AriaAbd1/Fume-Extracter/images/IMG_6583.jpg

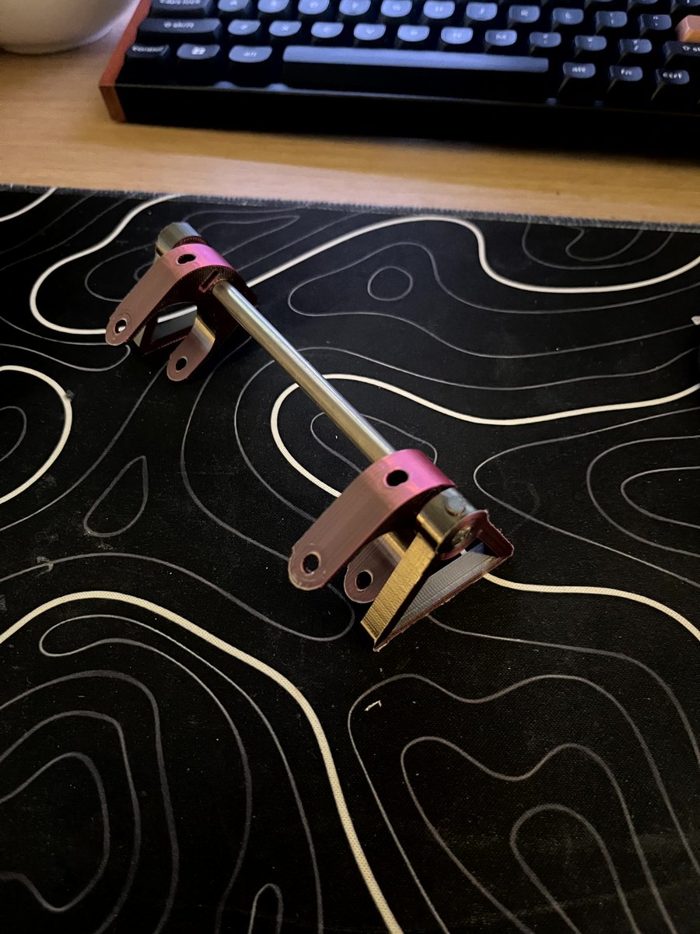
images/IMG_6583.jpg
