AriaAbd1/Fume-Extracter/images/IMG_6584.jpg

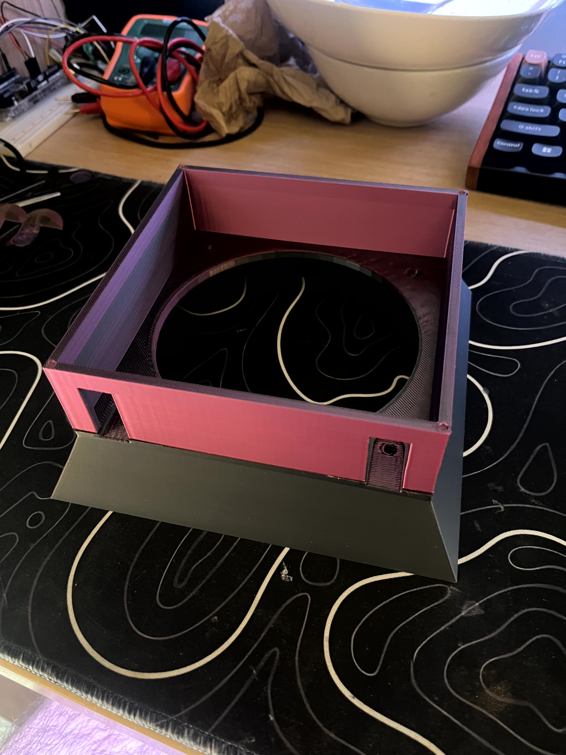
images/IMG_6584.jpg
