AriaAbd1/Fume-Extracter/images/IMG_6585.jpg

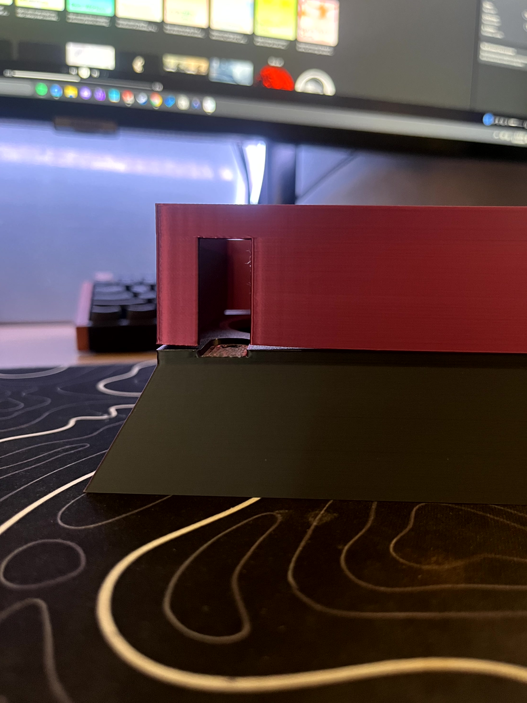
images/IMG_6585.jpg
