AriaAbd1/Fume-Extracter/images/IMG_6586.jpg

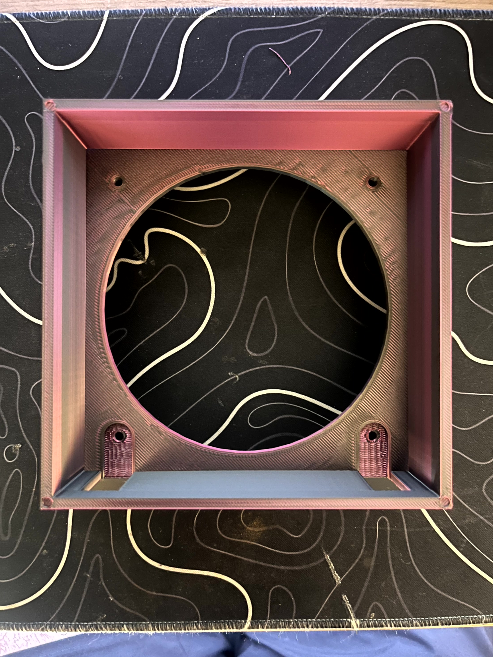
images/IMG_6586.jpg
