AriaAbd1/Fume-Extracter/images/IMG_6587.jpg

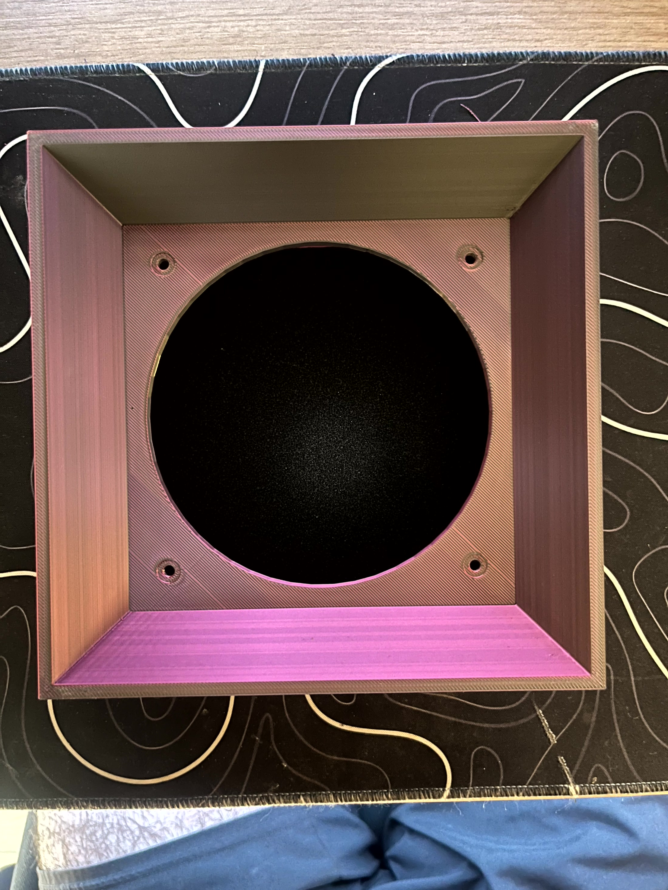
images/IMG_6587.jpg
