AriaAbd1/Fume-Extracter/images/IMG_6588.jpg

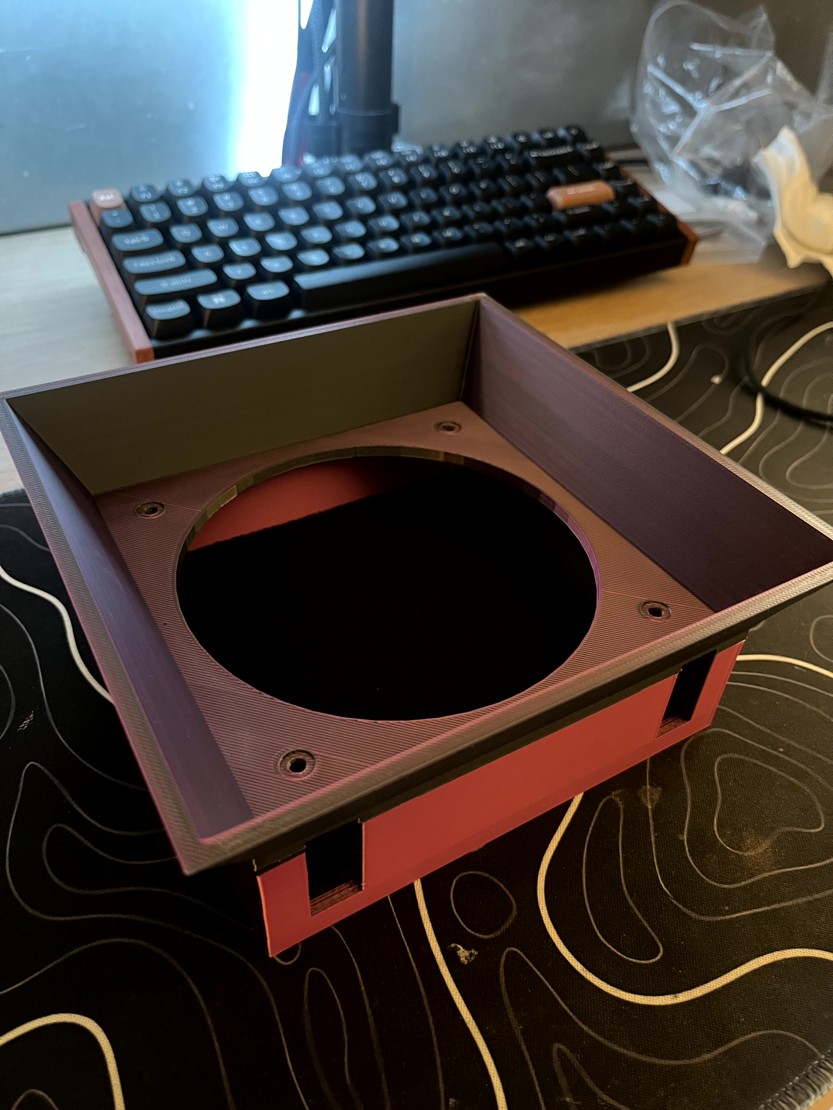
images/IMG_6588.jpg
