AriaAbd1/Fume-Extracter/images/IMG_6589.jpg

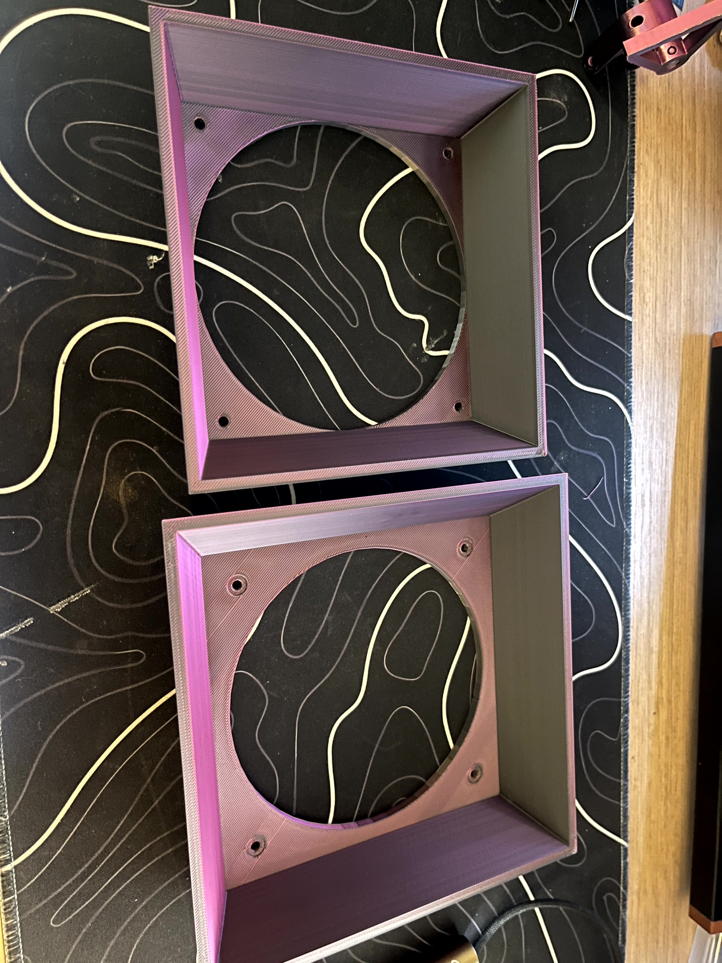
images/IMG_6589.jpg
