AriaAbd1/Fume-Extracter/images/IMG_6590.jpg

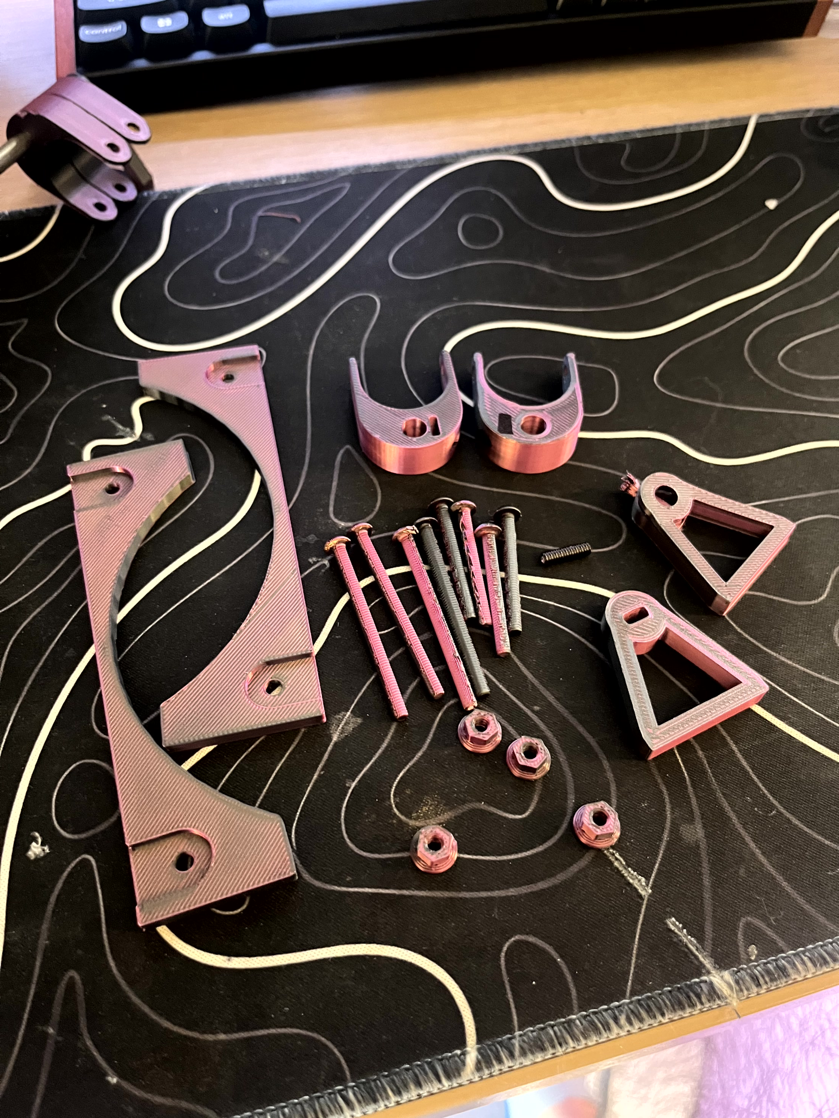
images/IMG_6590.jpg
