AriaAbd1/Fume-Extracter/images/IMG_6591.jpg

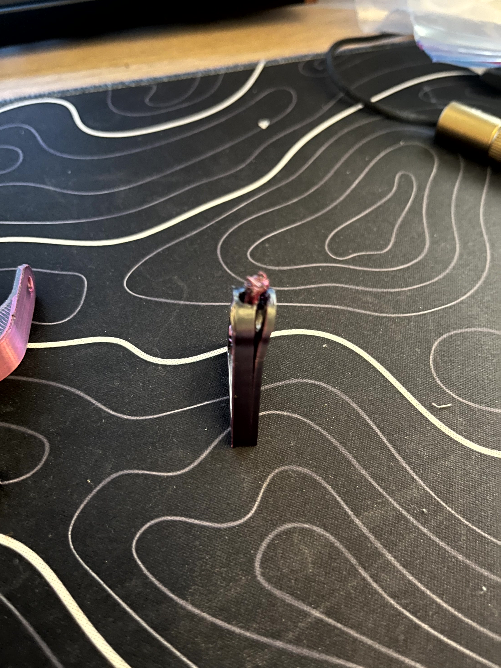
images/IMG_6591.jpg
