AriaAbd1/Fume-Extracter/images/IMG_6592.jpg

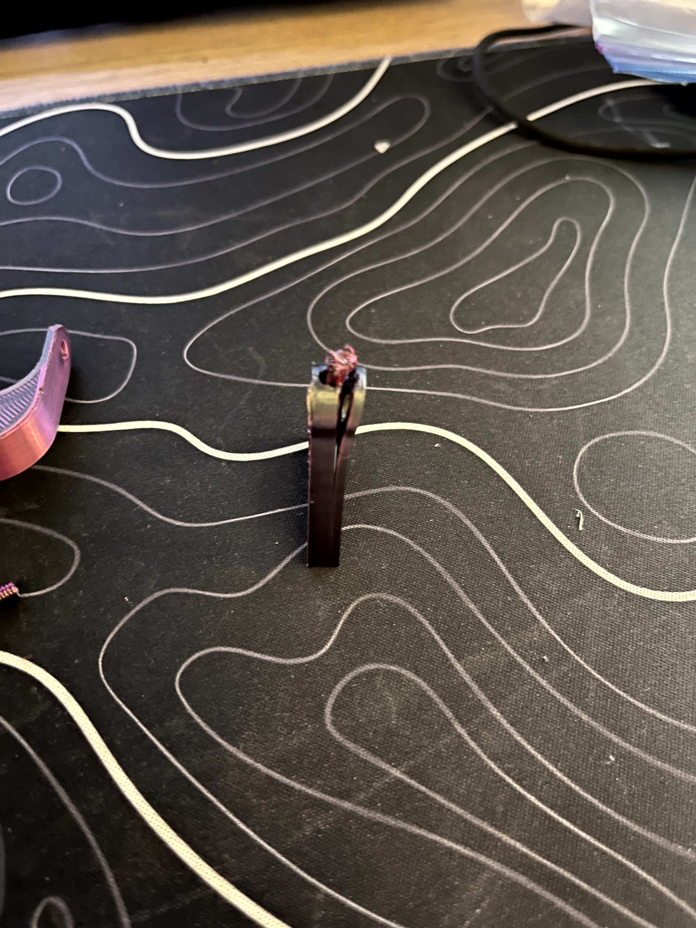
images/IMG_6592.jpg
