AriaAbd1/Fume-Extracter/images/IMG_6593.jpg

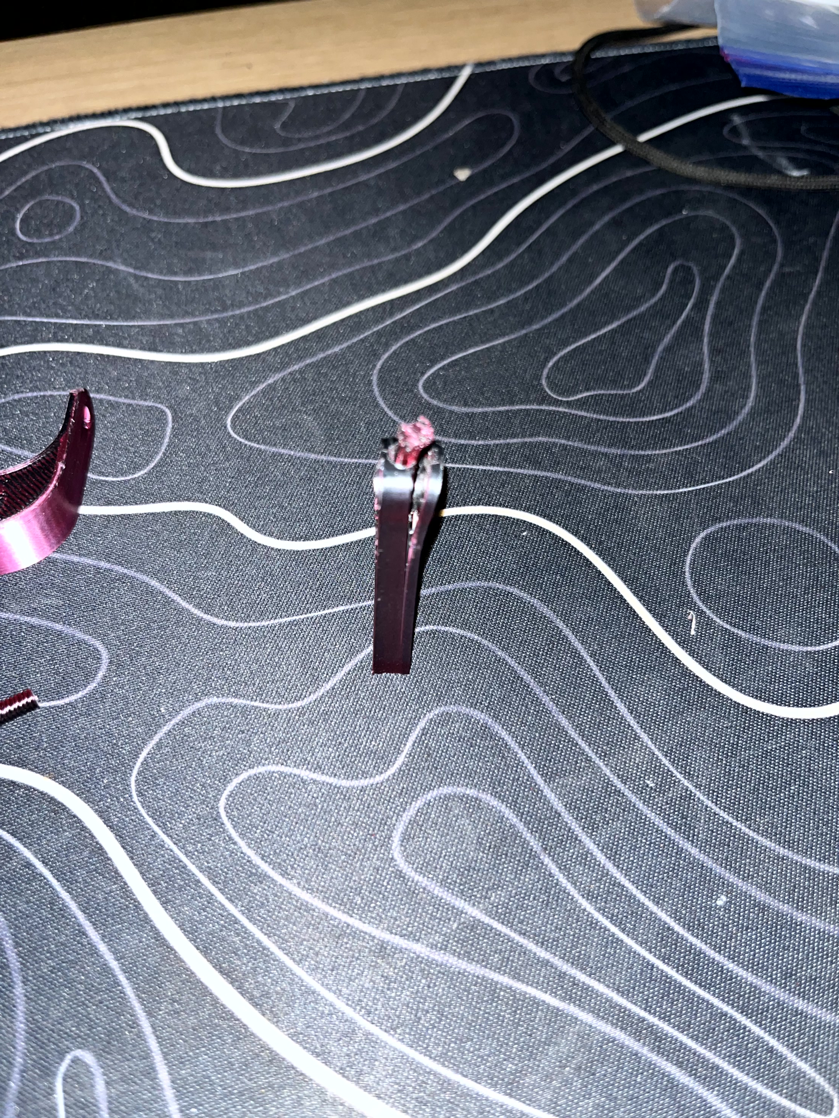
images/IMG_6593.jpg
