AriaAbd1/Fume-Extracter/images/IMG_6594.jpg

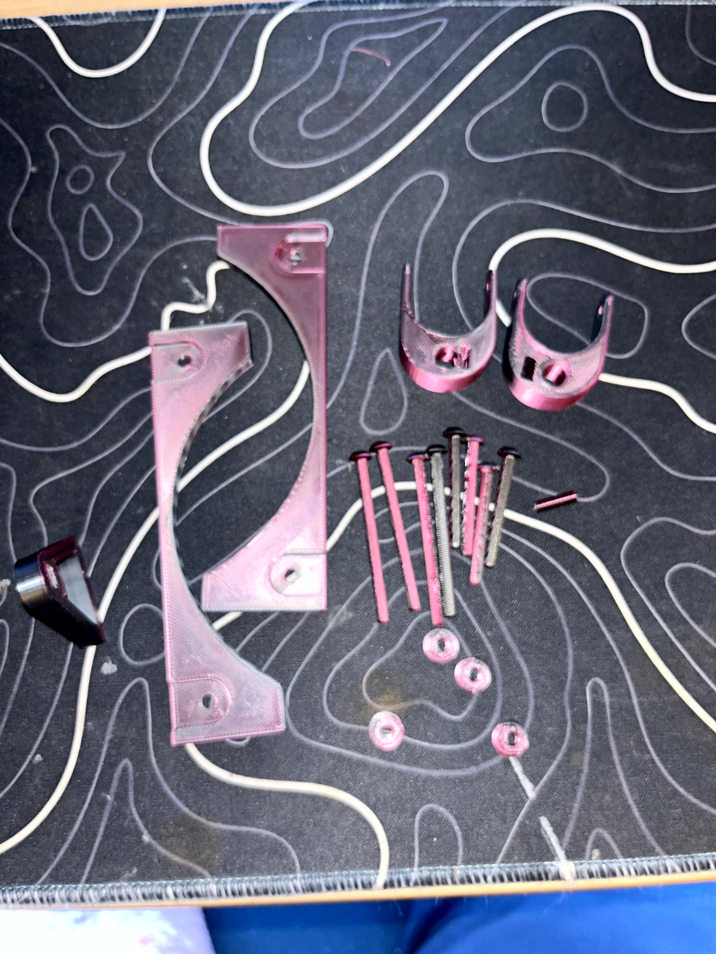
images/IMG_6594.jpg
