AriaAbd1/Fume-Extracter/images/IMG_6595.jpg

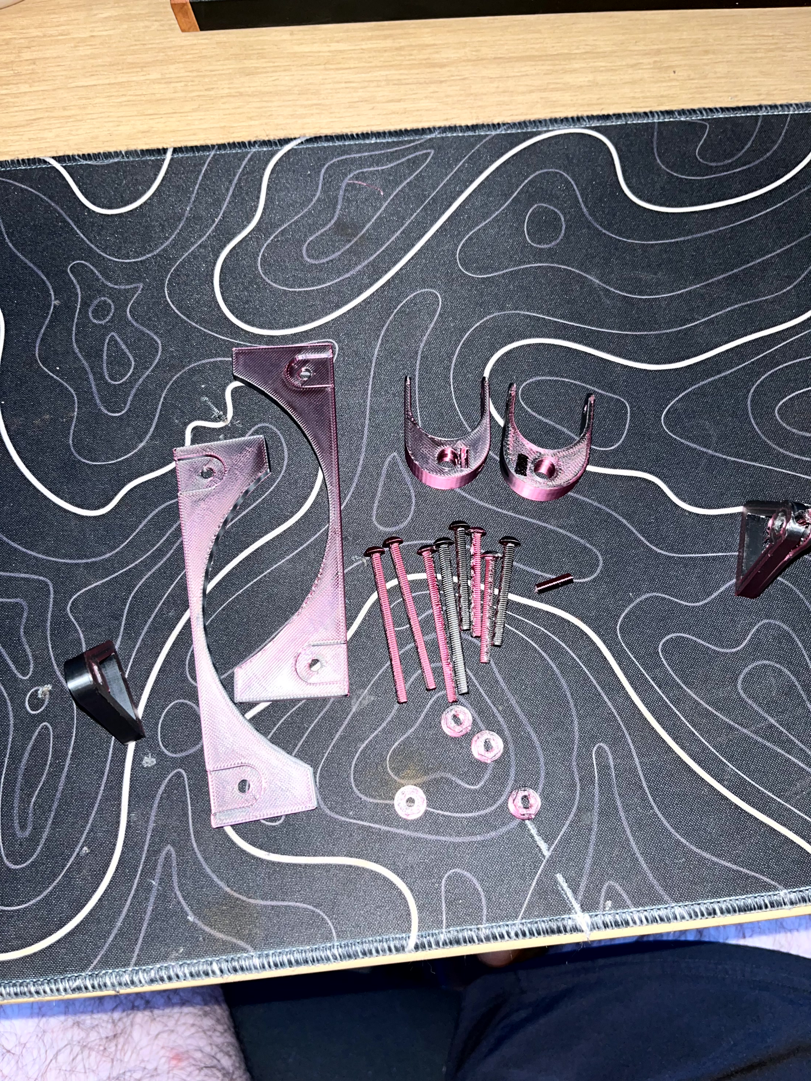
images/IMG_6595.jpg
