AriaAbd1/Fume-Extracter/images/IMG_6596.jpg

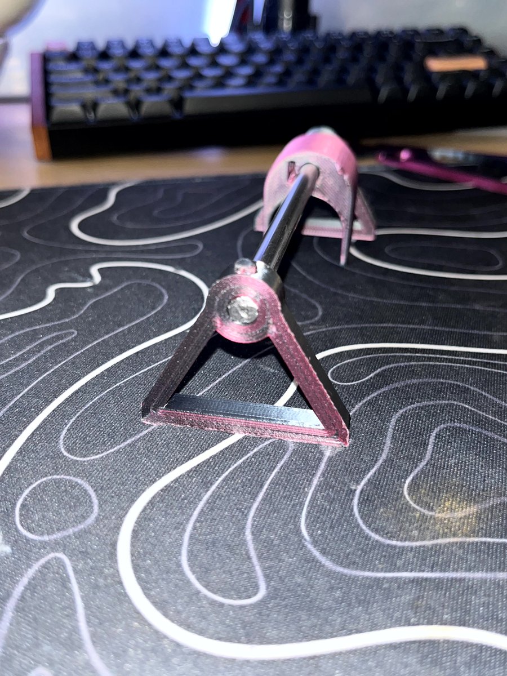
images/IMG_6596.jpg
