AriaAbd1/Fume-Extracter/images/IMG_6597.jpg

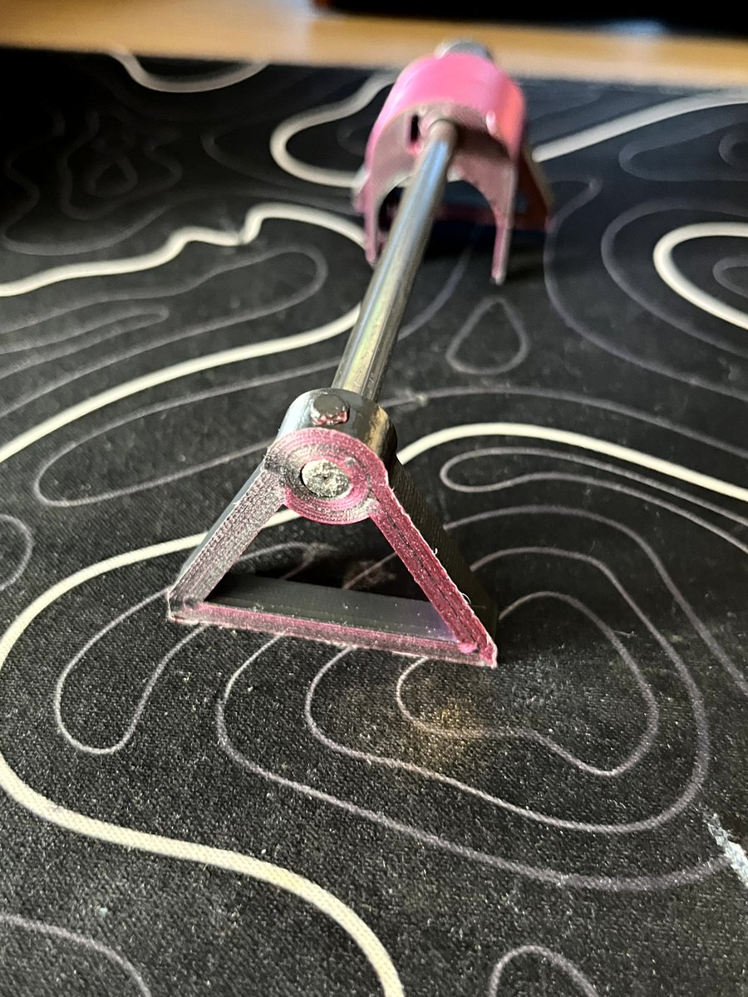
images/IMG_6597.jpg
