AriaAbd1/Fume-Extracter/images/IMG_6598.jpg

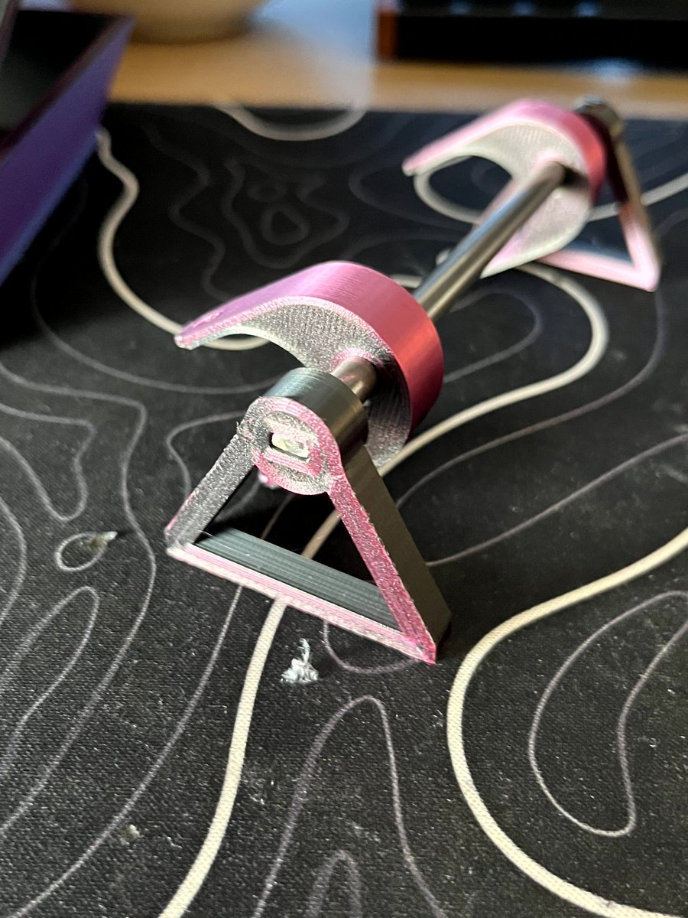
images/IMG_6598.jpg
