AriaAbd1/Fume-Extracter/images/IMG_6599.jpg

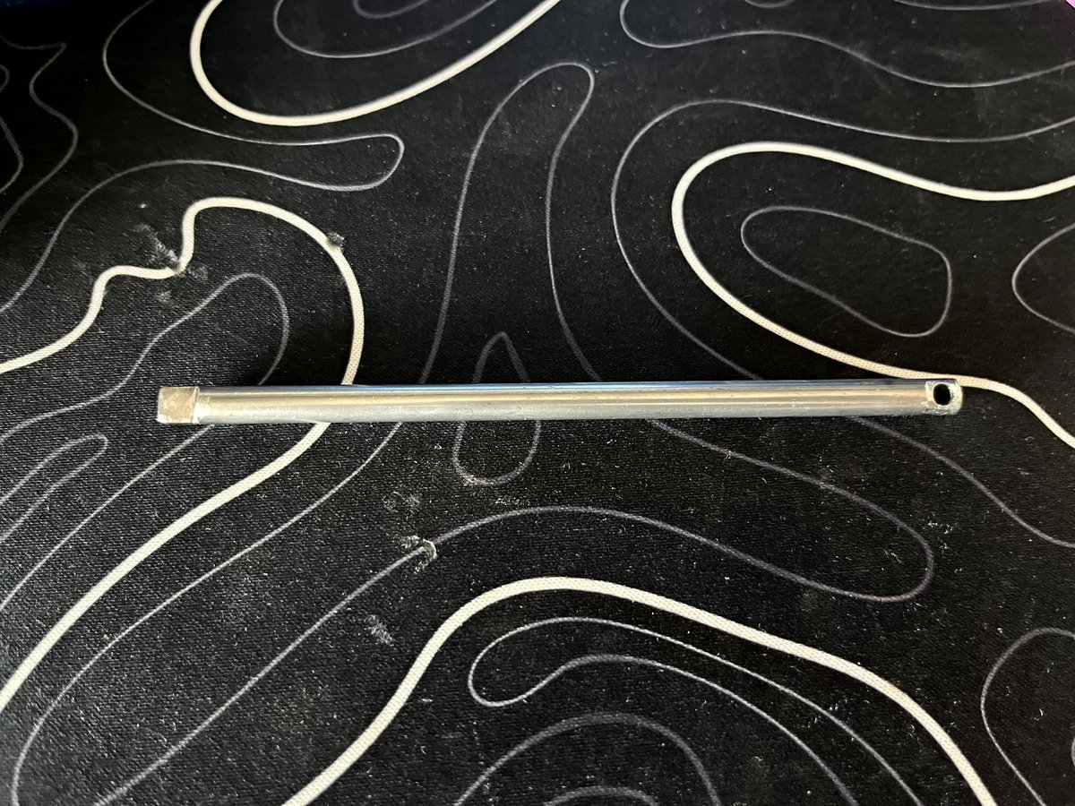
images/IMG_6599.jpg
