AriaAbd1/Fume-Extracter/images/IMG_6600.jpg

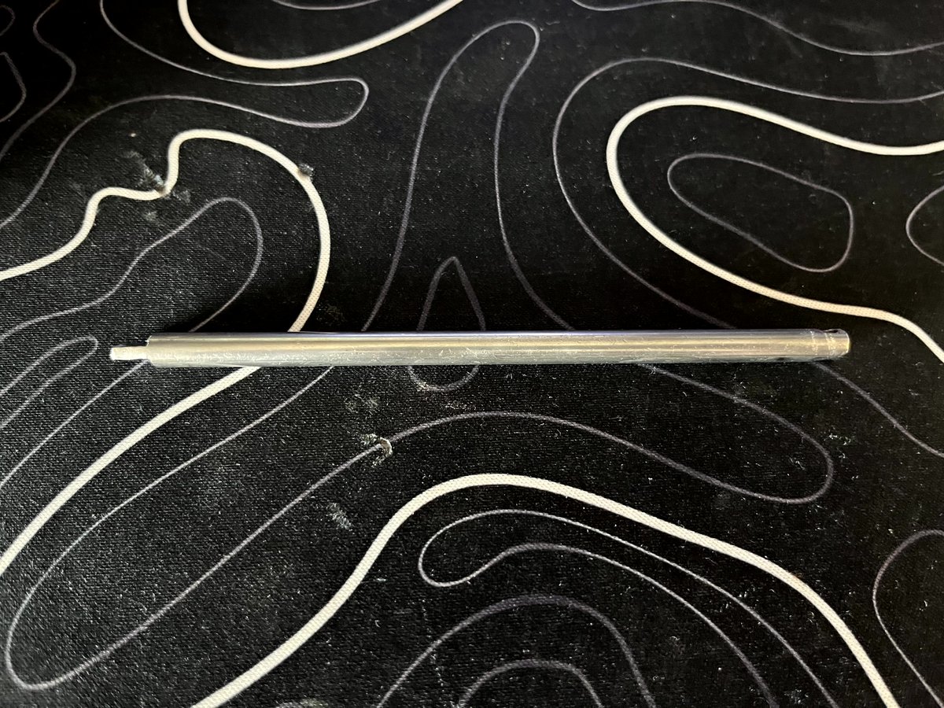
images/IMG_6600.jpg
