AriaAbd1/Fume-Extracter/images/IMG_6601.jpg

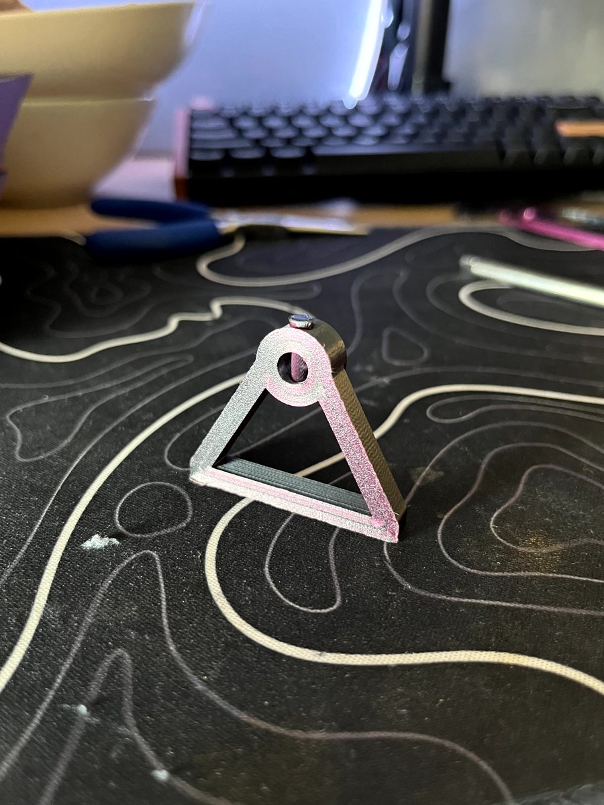
images/IMG_6601.jpg
