AriaAbd1/Fume-Extracter/images/IMG_6602.jpg

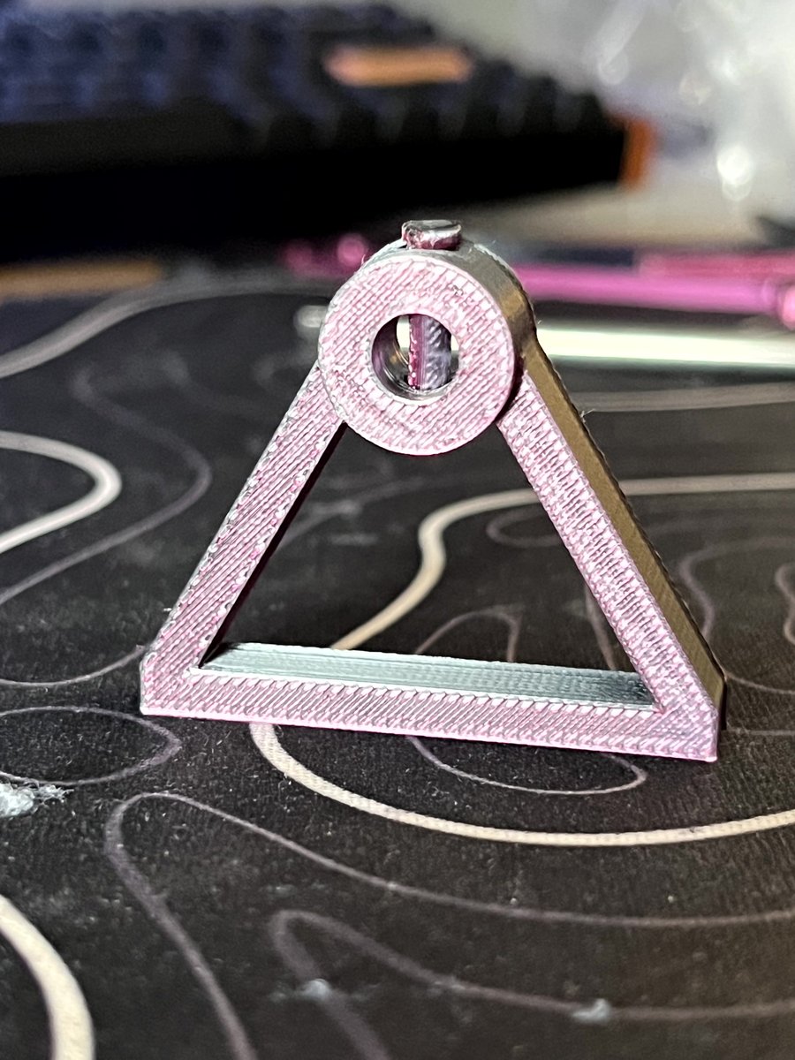
images/IMG_6602.jpg
