AriaAbd1/Fume-Extracter/images/IMG_6603.jpg

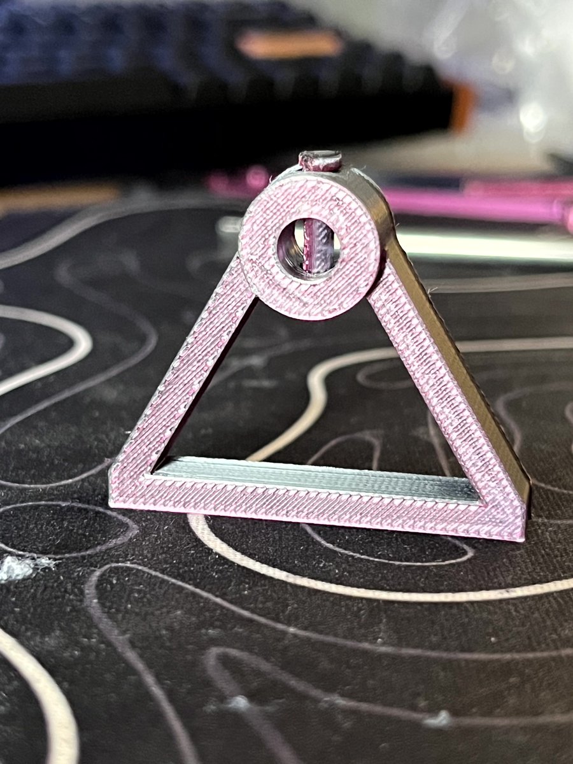
images/IMG_6603.jpg
