AriaAbd1/Fume-Extracter/images/IMG_6604.jpg

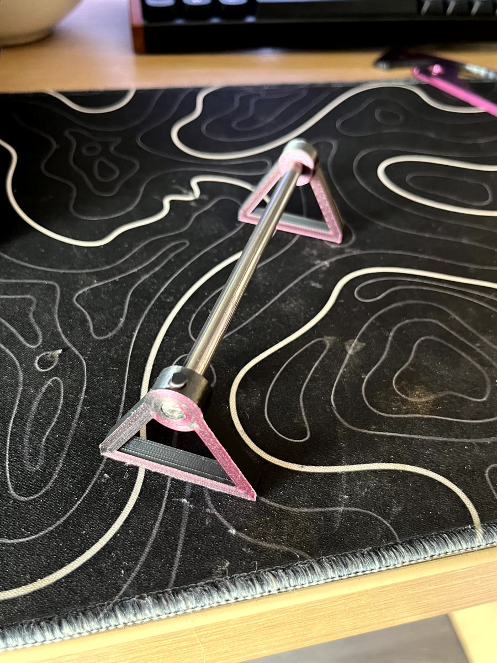
images/IMG_6604.jpg
