AriaAbd1/Fume-Extracter/images/IMG_6618.jpg

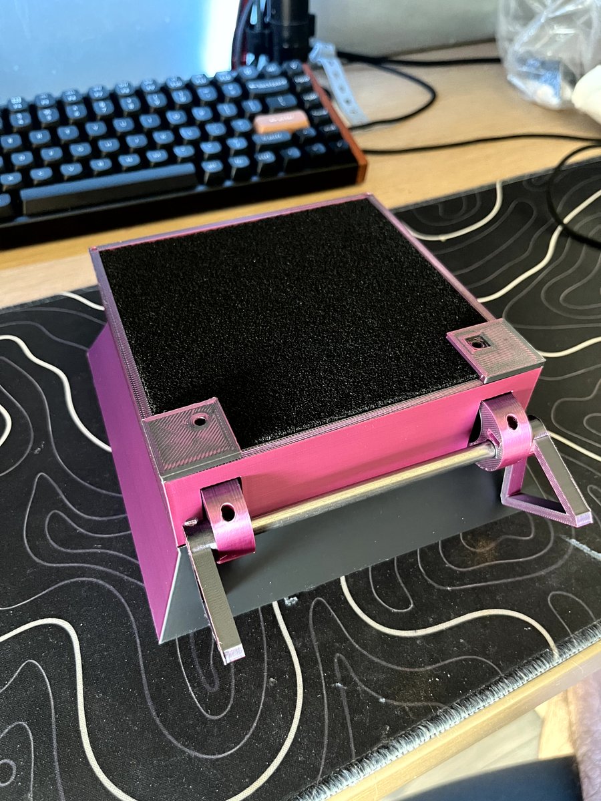
images/IMG_6618.jpg
