AriaAbd1/Fume-Extracter/images/IMG_6619.jpg

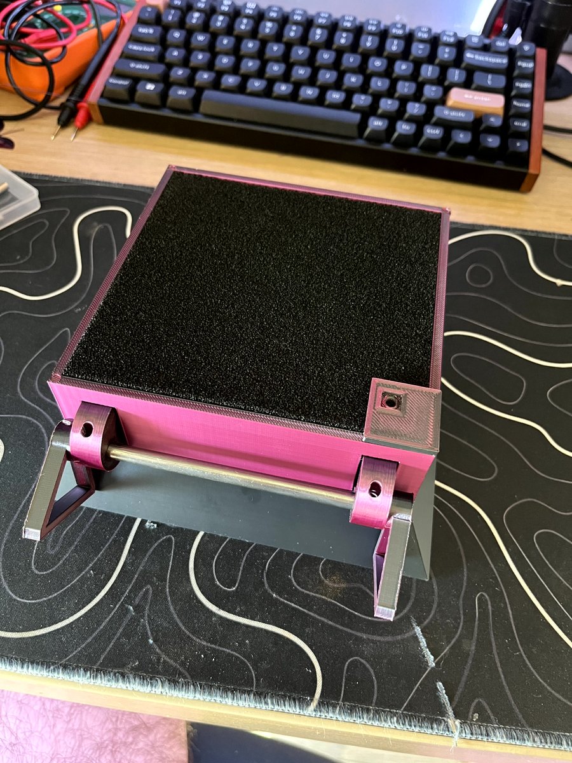
images/IMG_6619.jpg
