AriaAbd1/Fume-Extracter/images/IMG_6620.jpg

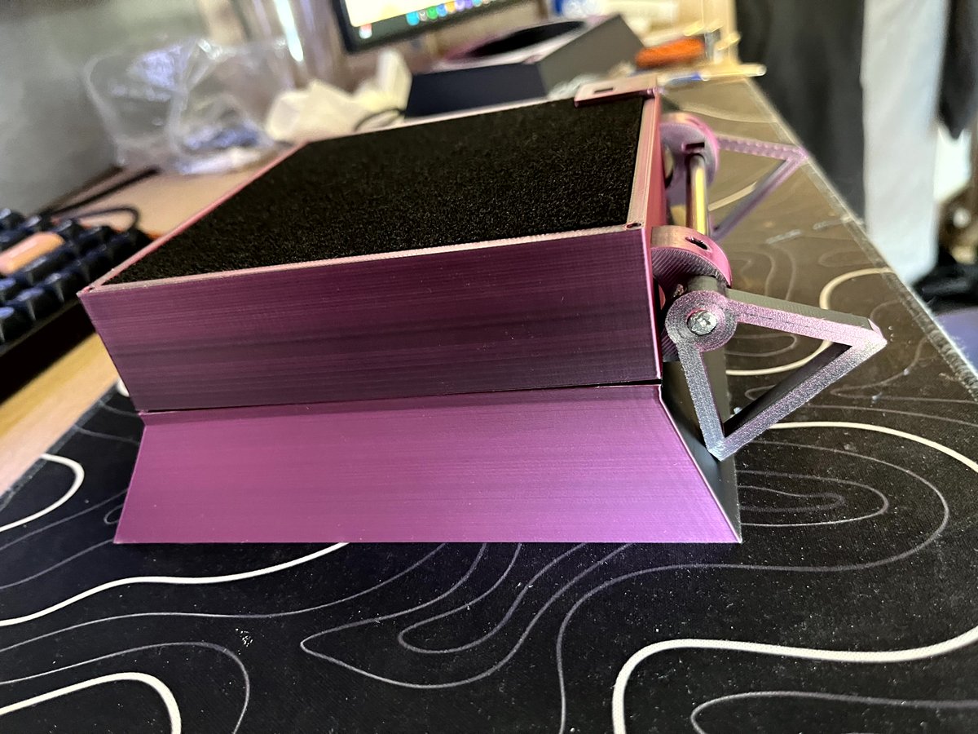
images/IMG_6620.jpg
