AriaAbd1/Fume-Extracter/images/IMG_6621.jpg

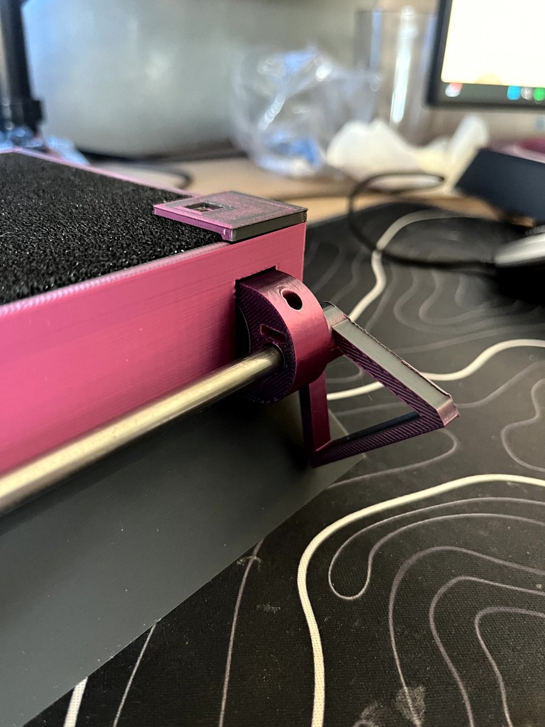
images/IMG_6621.jpg
