AriaAbd1/Fume-Extracter/images/IMG_6622.jpg

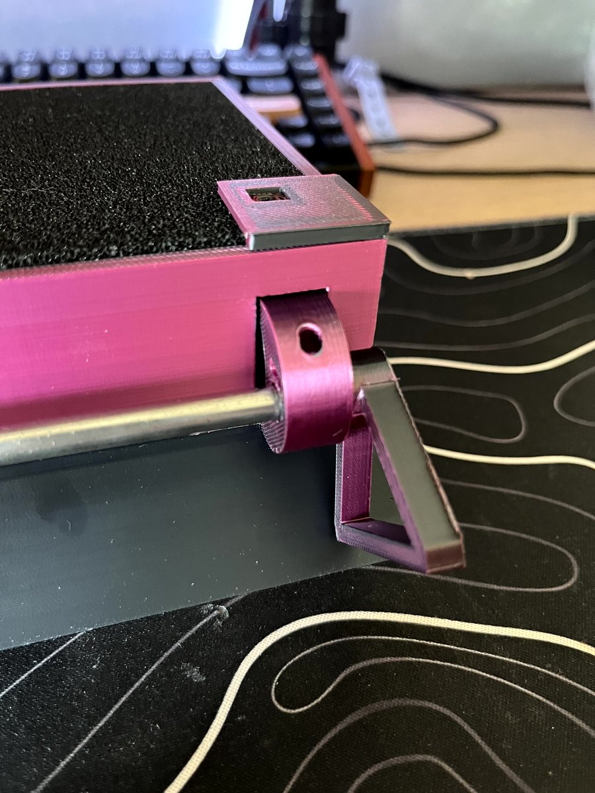
images/IMG_6622.jpg
