AriaAbd1/Fume-Extracter/images/IMG_6623.jpg

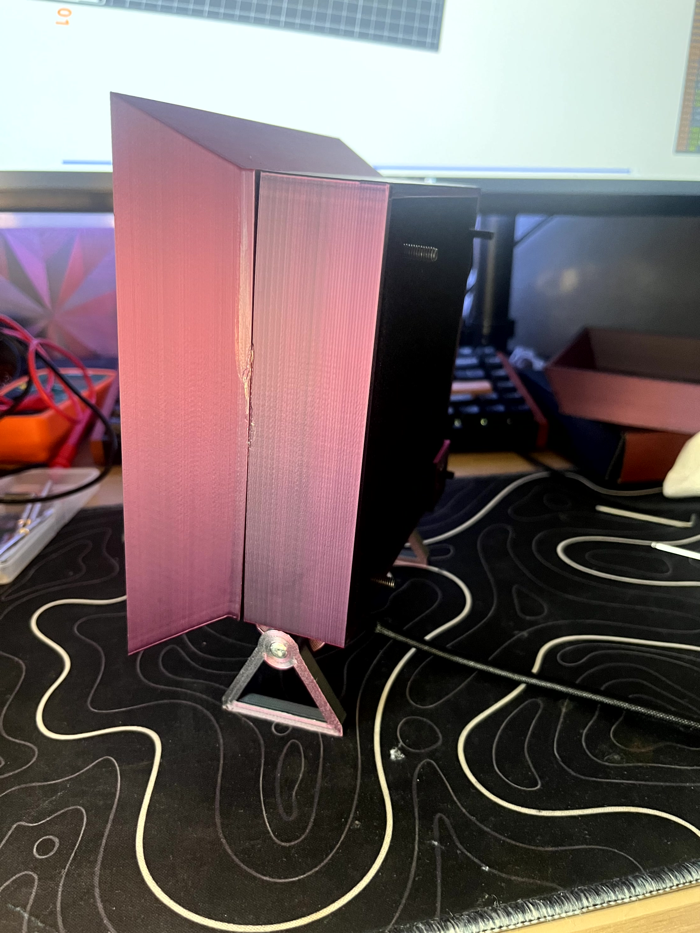
images/IMG_6623.jpg
