AriaAbd1/Fume-Extracter/images/IMG_6624.jpg

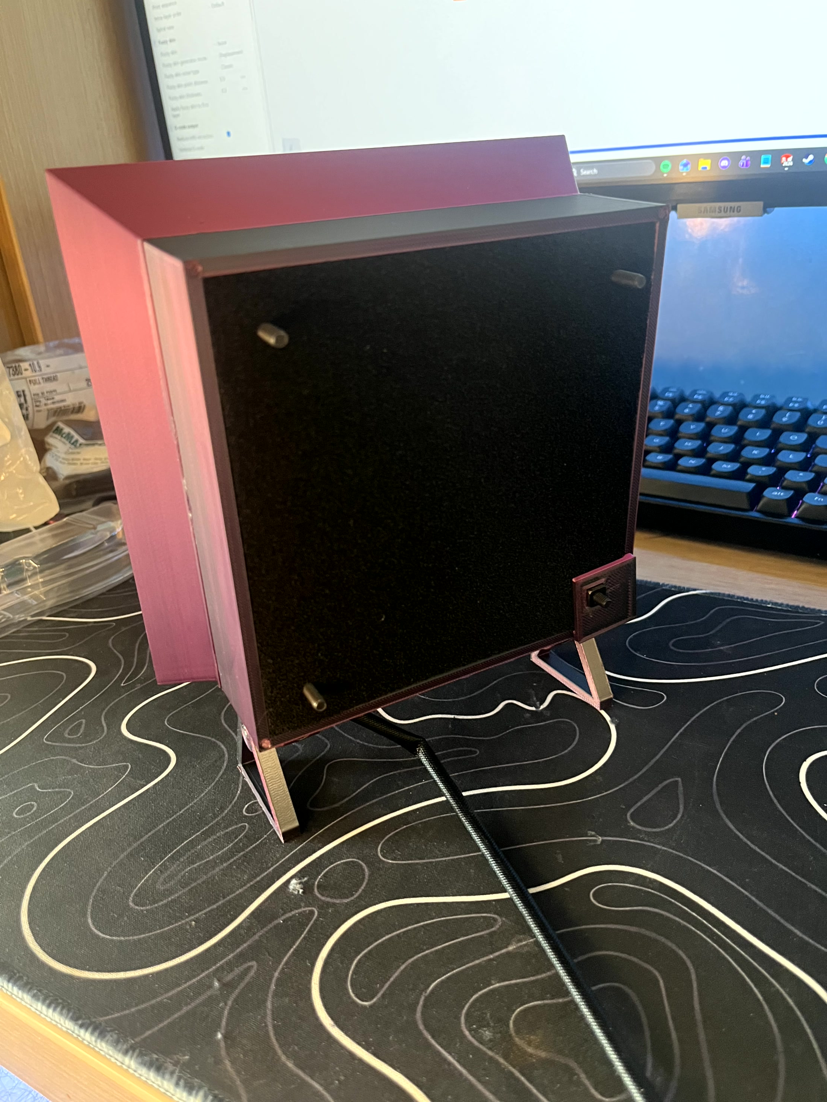
images/IMG_6624.jpg
