AriaAbd1/Fume-Extracter/images/IMG_6625.jpg

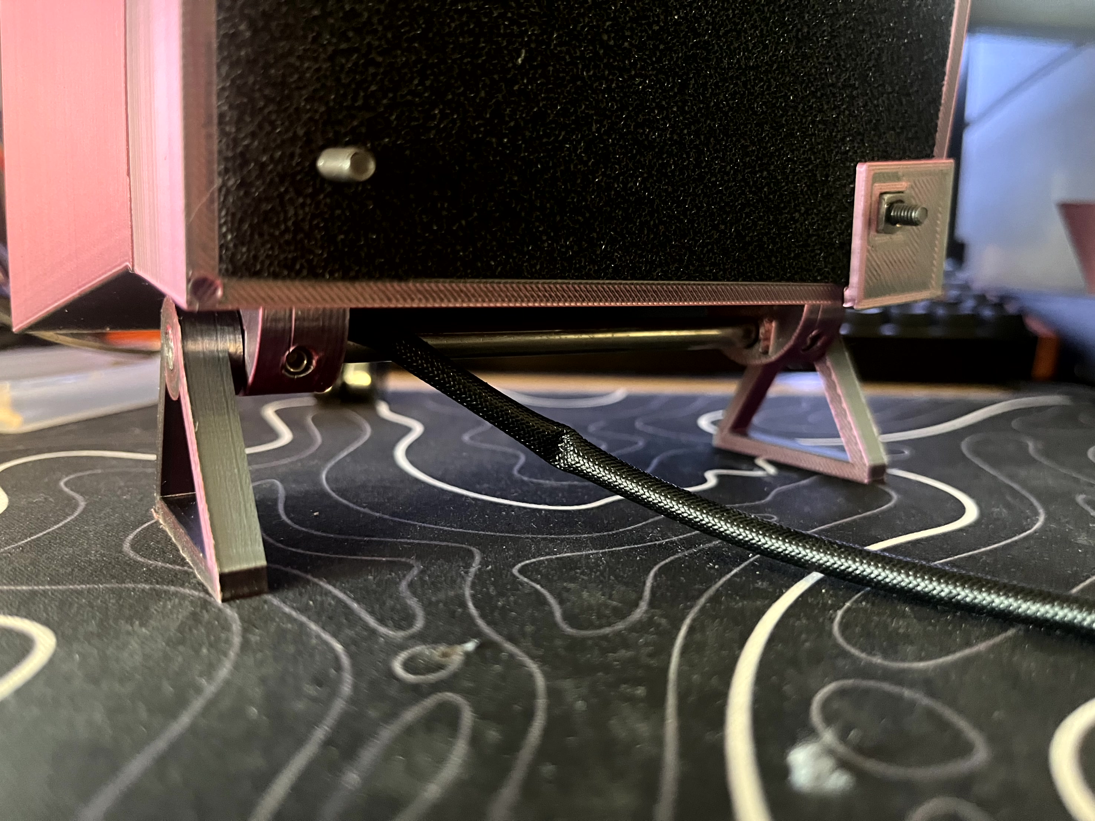
images/IMG_6625.jpg
