AriaAbd1/Fume-Extracter/images/IMG_6626.jpg

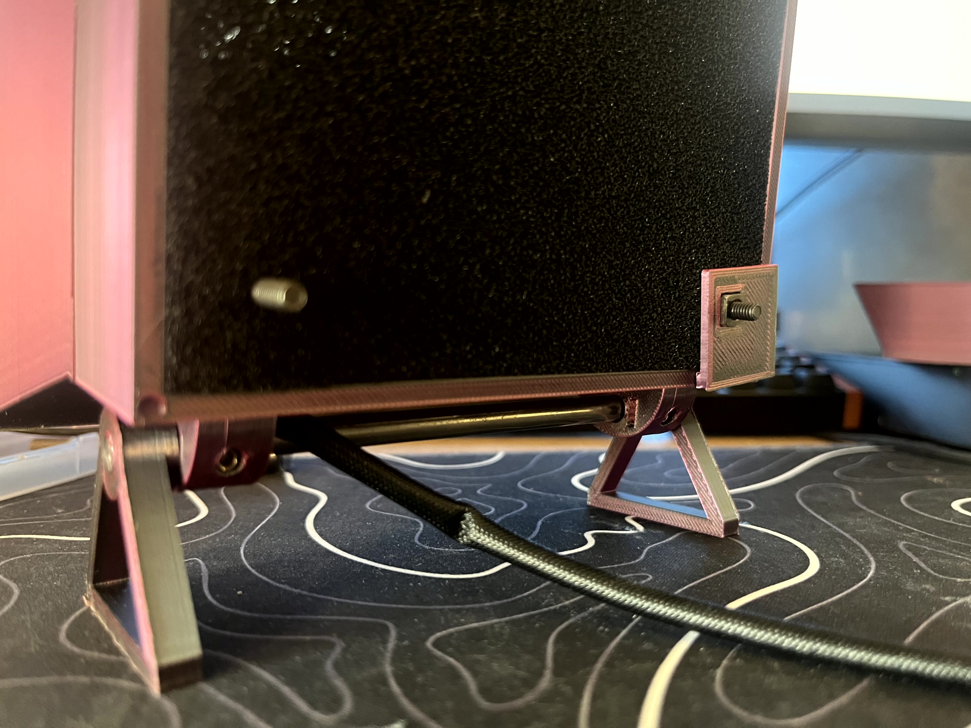
images/IMG_6626.jpg
