AriaAbd1/Fume-Extracter/images/IMG_6627.jpg

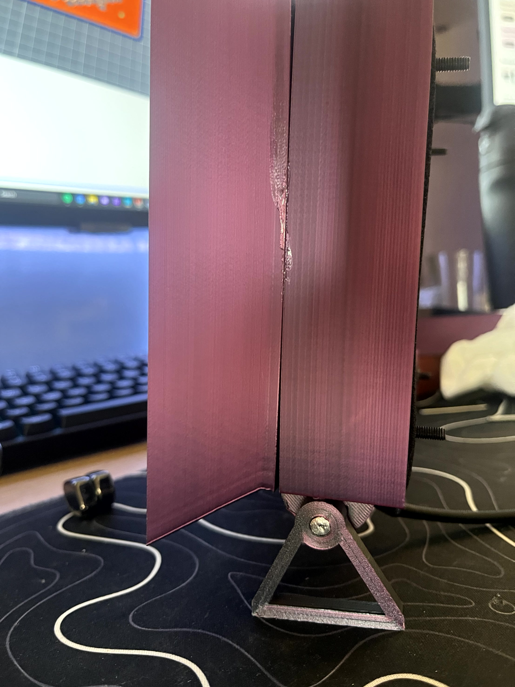
images/IMG_6627.jpg
