AriaAbd1/Fume-Extracter/images/IMG_6628.jpg

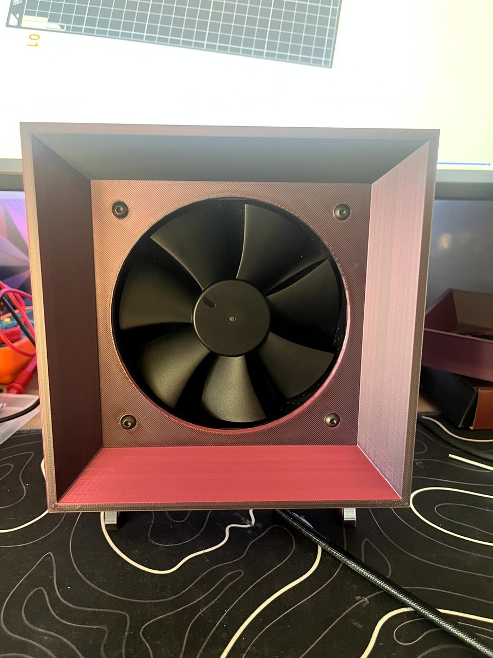
images/IMG_6628.jpg
