AriaAbd1/Fume-Extracter/images/IMG_6629.jpg

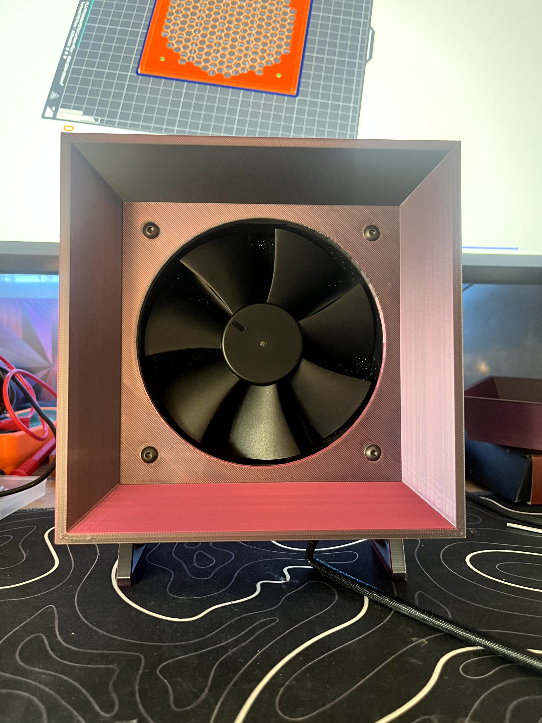
images/IMG_6629.jpg
