AriaAbd1/Fume-Extracter/images/IMG_6630.jpg

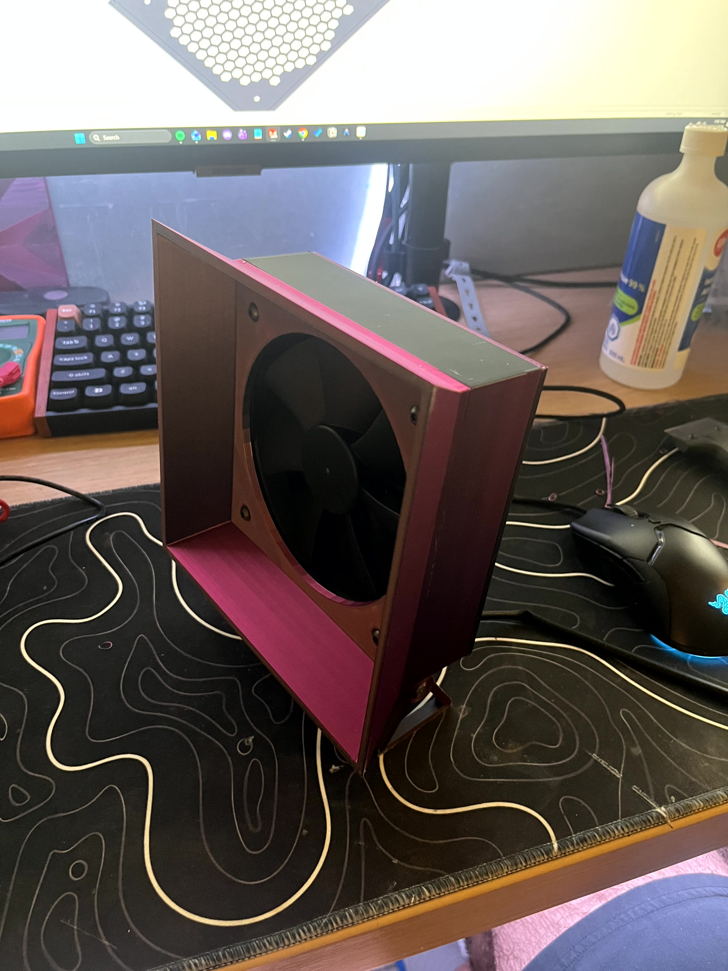
images/IMG_6630.jpg
