AriaAbd1/Fume-Extracter/images/IMG_6631.jpg

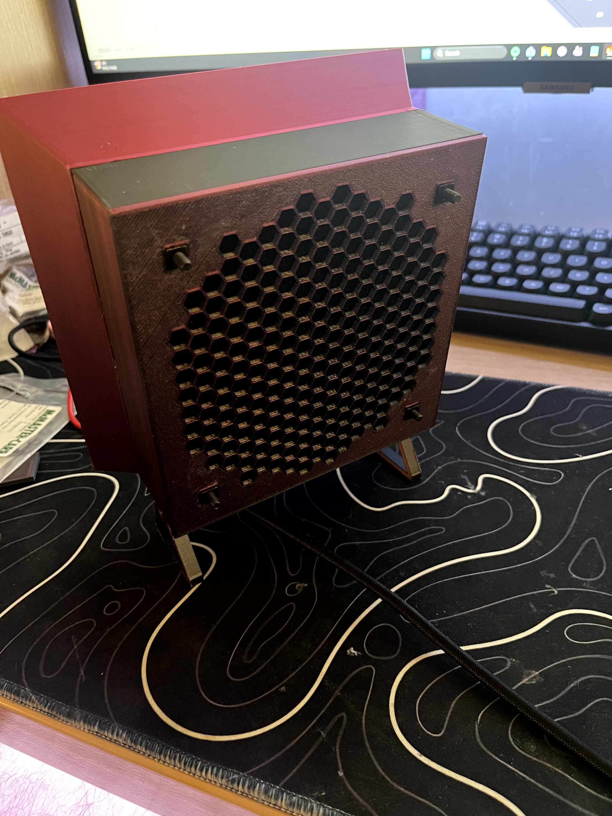
images/IMG_6631.jpg
