AriaAbd1/Fume-Extracter/images/IMG_6632.jpg

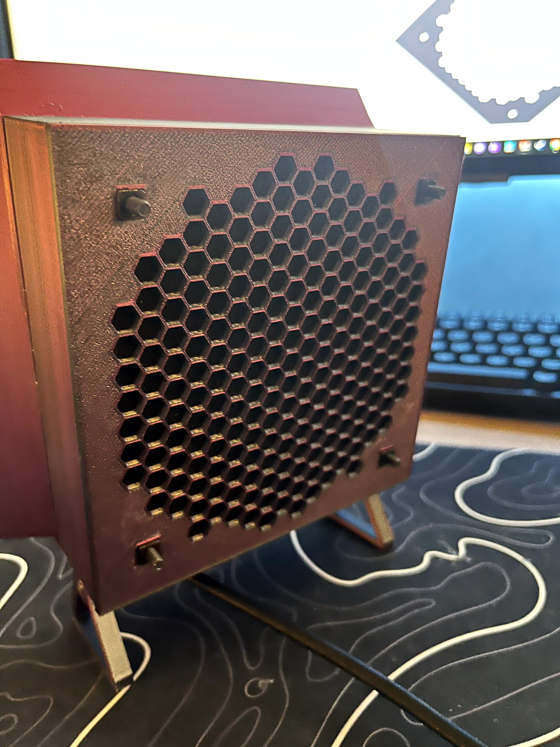
images/IMG_6632.jpg
