AriaAbd1/Fume-Extracter/images/IMG_6633.jpg

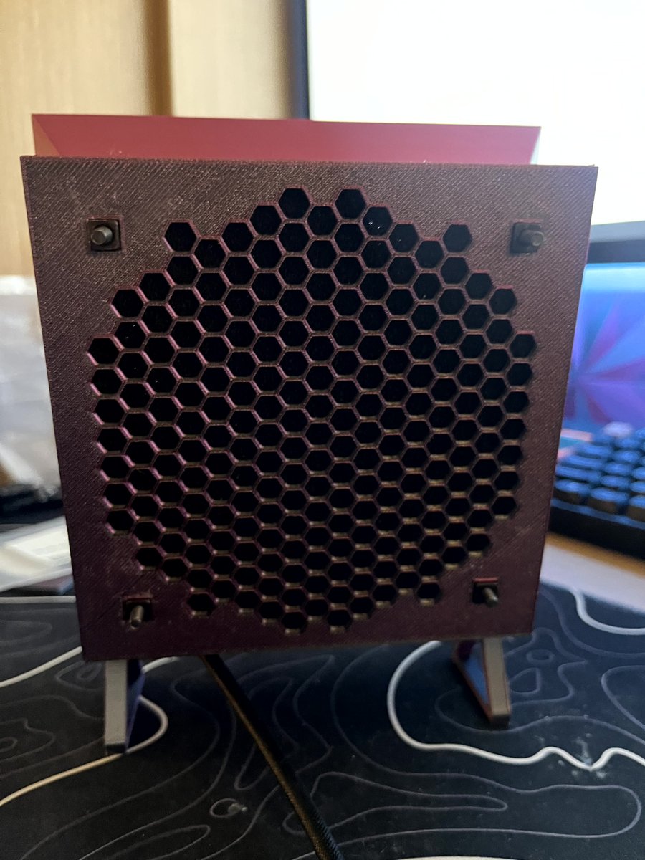
images/IMG_6633.jpg
