AriaAbd1/Fume-Extracter/images/IMG_6634.jpg

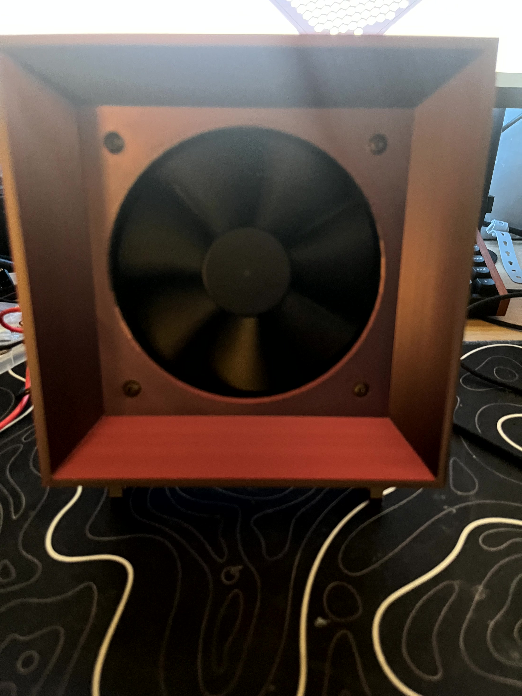
images/IMG_6634.jpg
