AriaAbd1/Fume-Extracter/images/IMG_6635.jpg

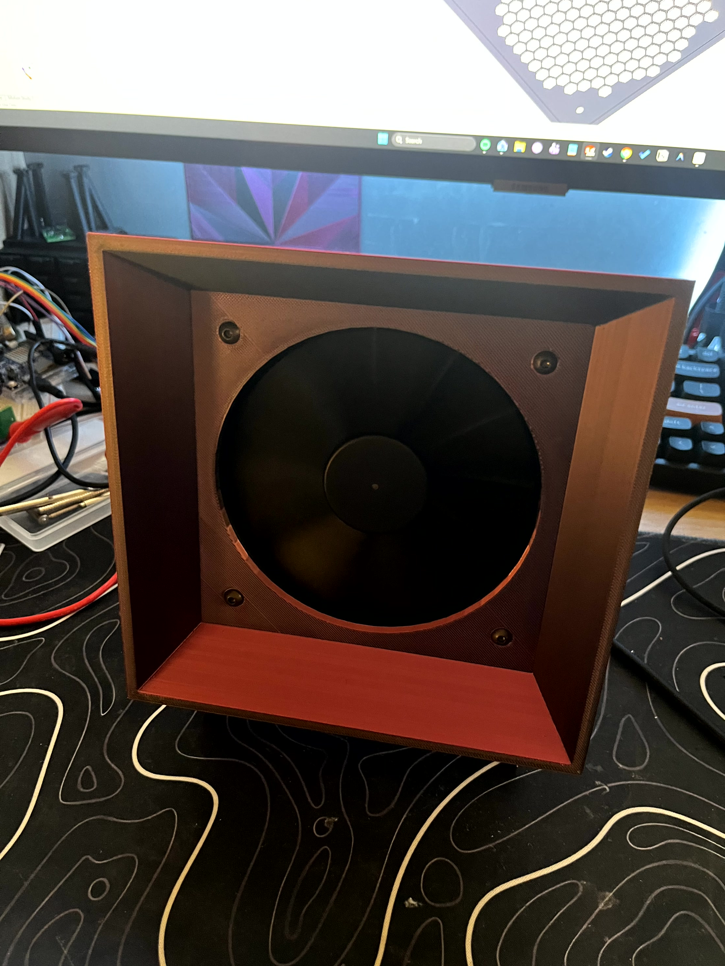
images/IMG_6635.jpg
