AriaAbd1/Fume-Extracter/images/IMG_6637.jpg

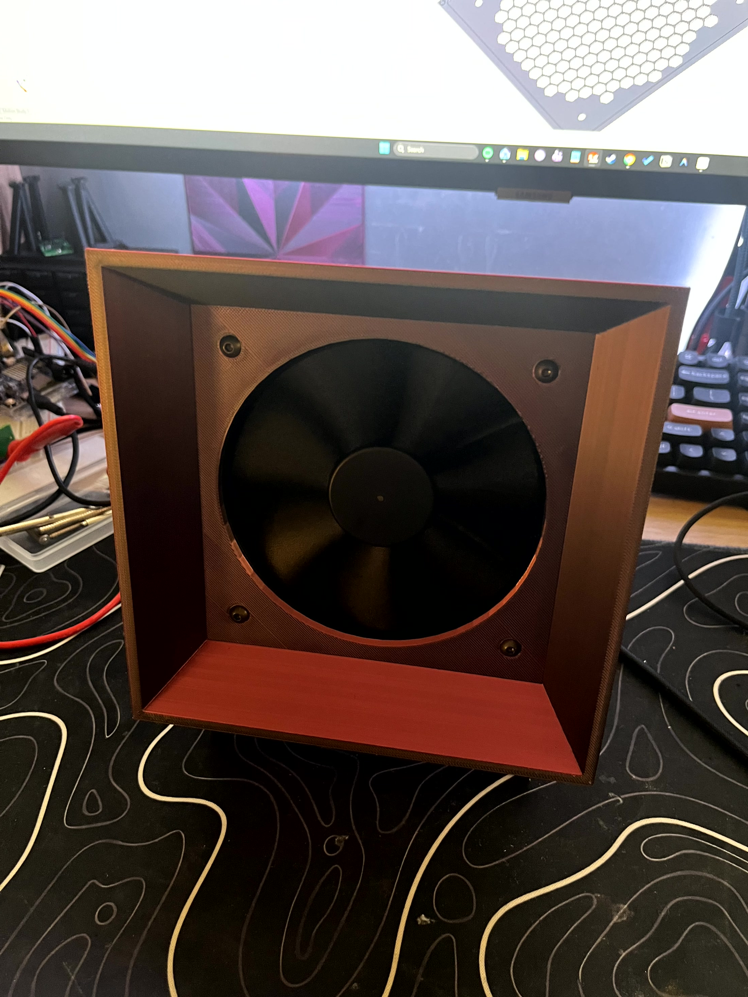
images/IMG_6637.jpg
