AriaAbd1/Fume-Extracter/images/IMG_6640.jpg

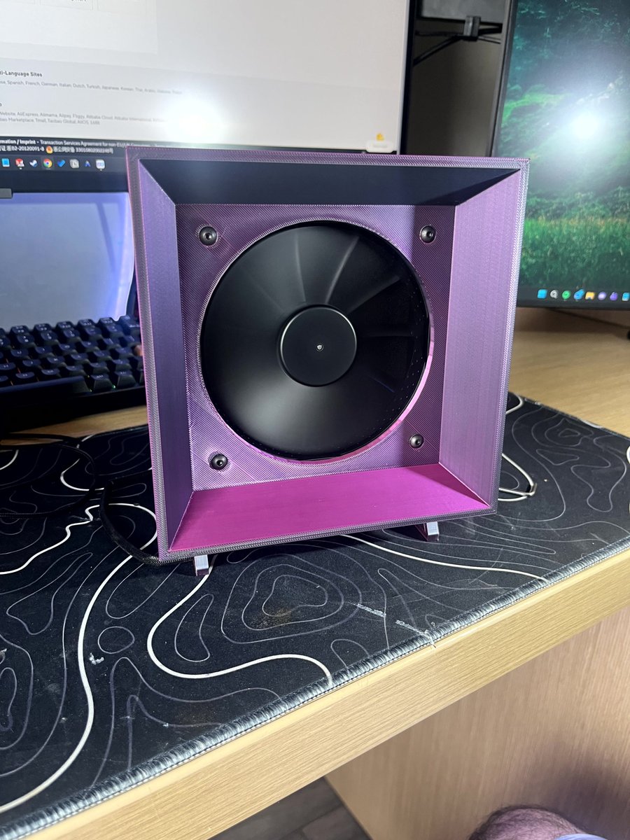
images/IMG_6640.jpg
