AriaAbd1/Fume-Extracter/images/IMG_6641.jpg

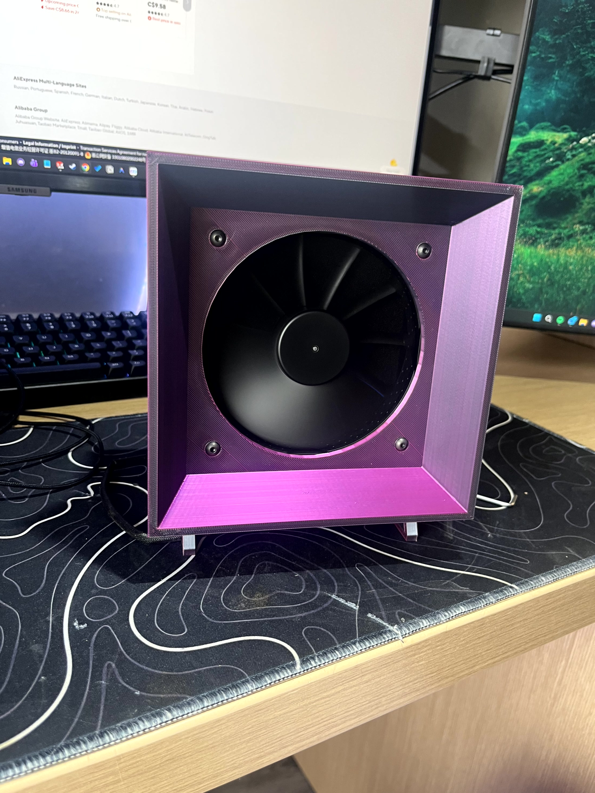
images/IMG_6641.jpg
