AriaAbd1/Fume-Extracter/images/IMG_6642.jpg

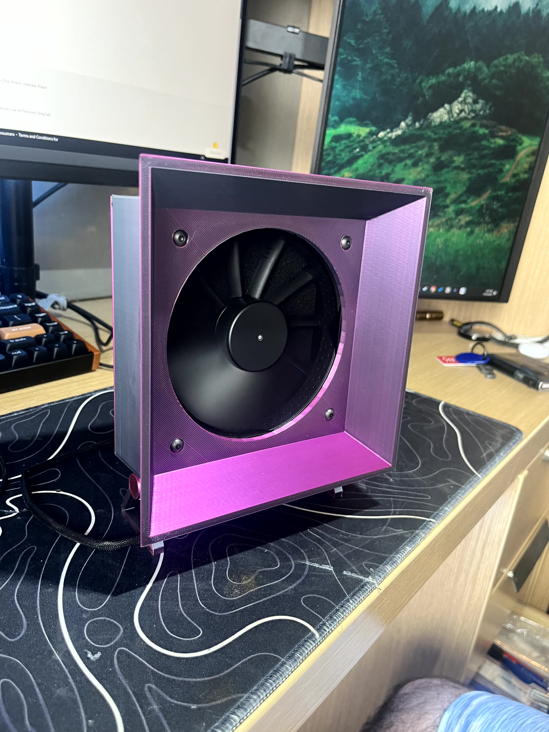
images/IMG_6642.jpg
