AriaAbd1/Fume-Extracter/images/IMG_6644.jpg

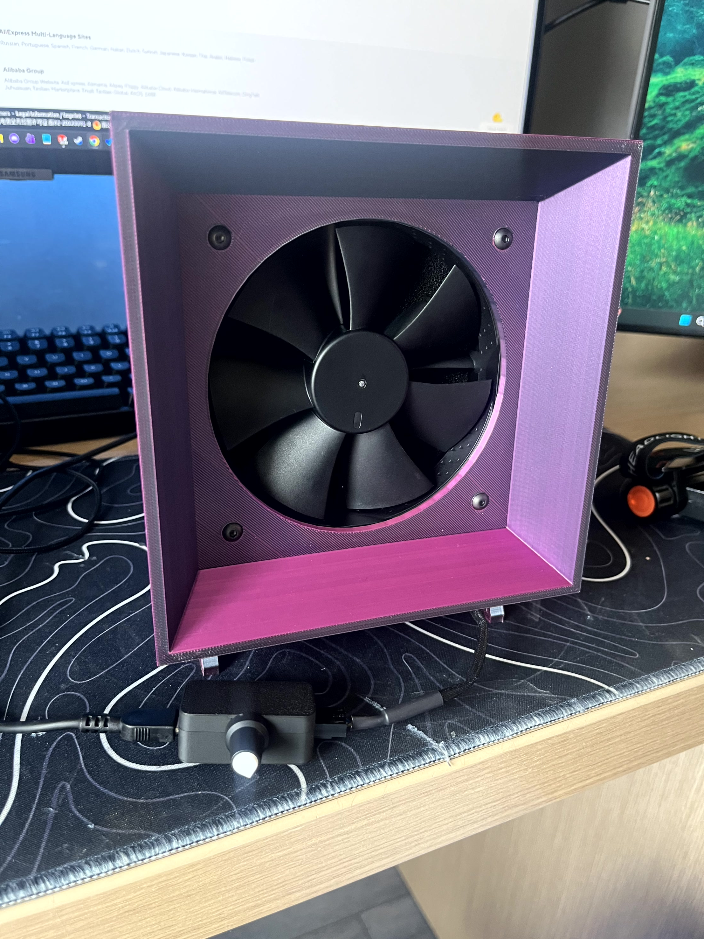
images/IMG_6644.jpg
