AriaAbd1/Fume-Extracter/images/IMG_6749.jpeg

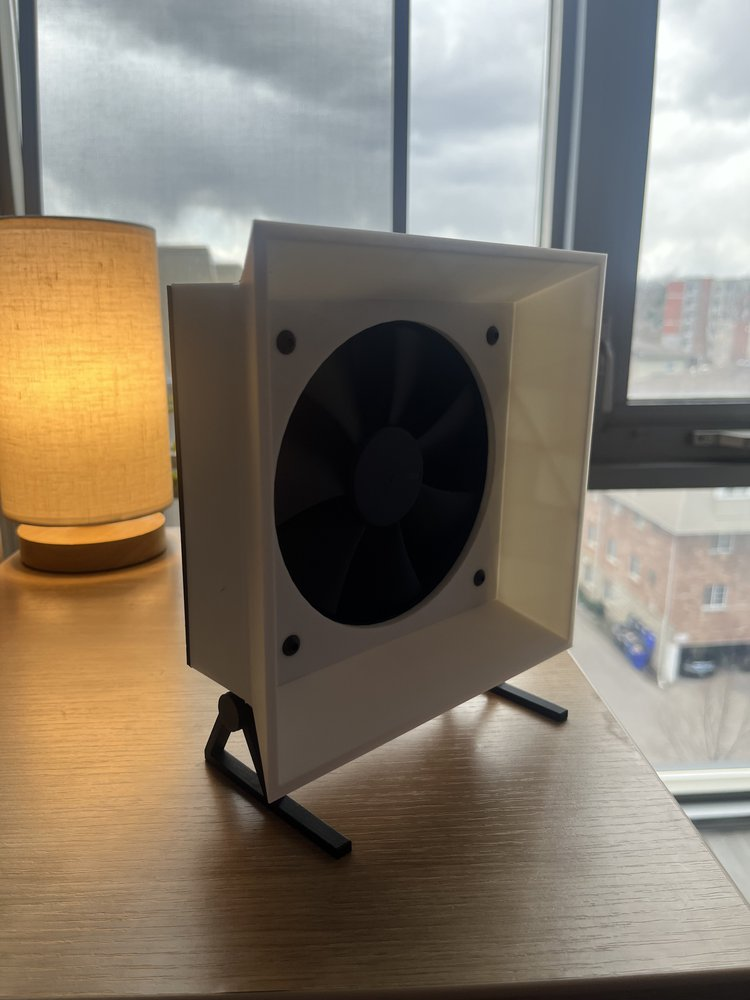
images/IMG_6749.jpeg
