AriaAbd1/Fume-Extracter/images/IMG_6750.jpeg

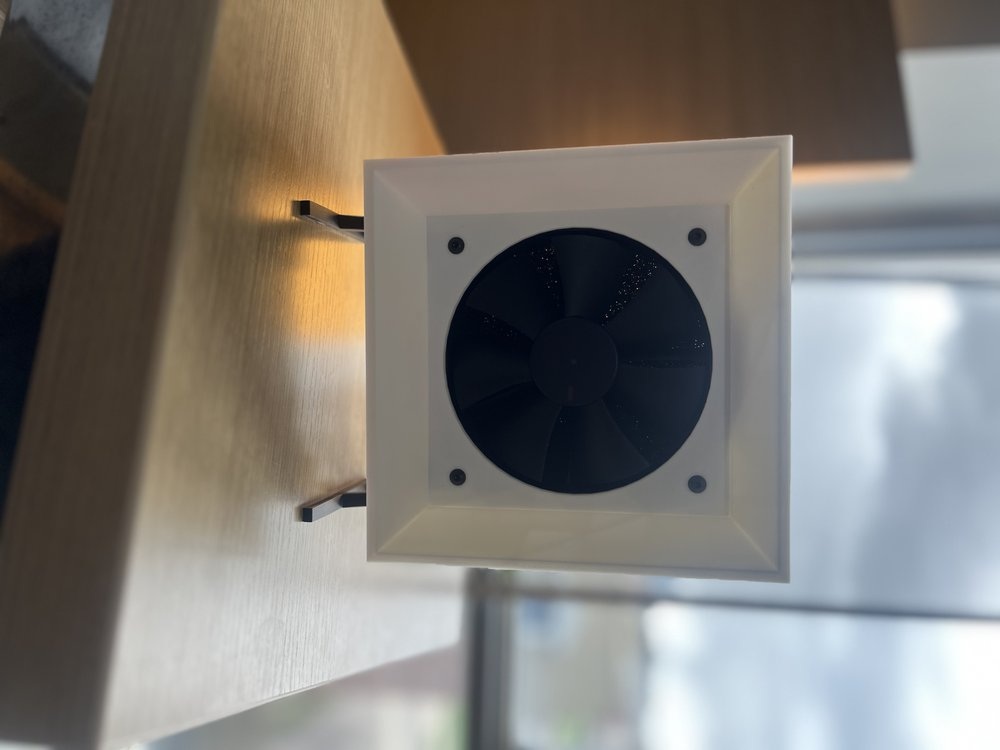
images/IMG_6750.jpeg
