AriaAbd1/Fume-Extracter/images/IMG_6751.jpeg

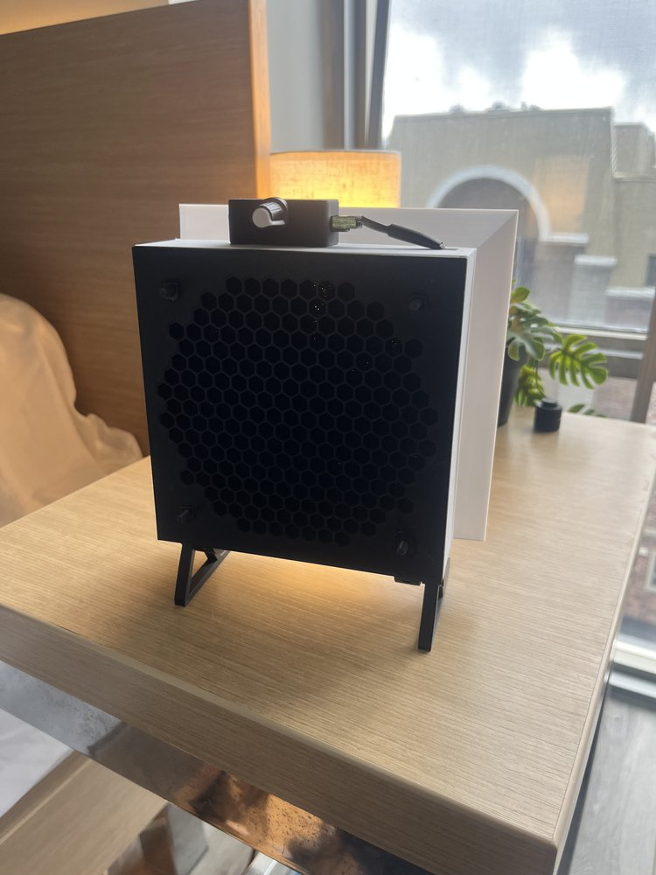
images/IMG_6751.jpeg
