AriaAbd1/Fume-Extracter/images/IMG_6752.jpeg

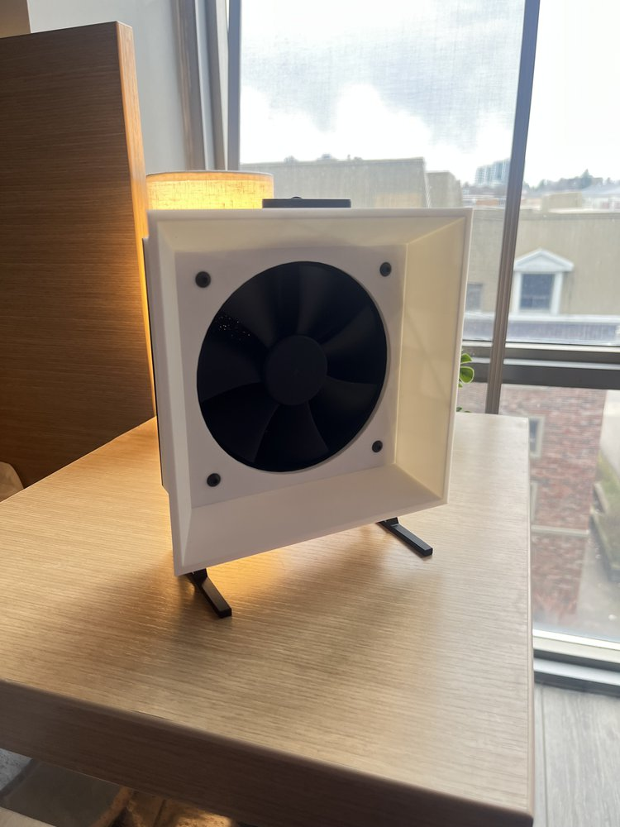
images/IMG_6752.jpeg
