AriaAbd1/Fume-Extracter/images/IMG_6753.jpeg

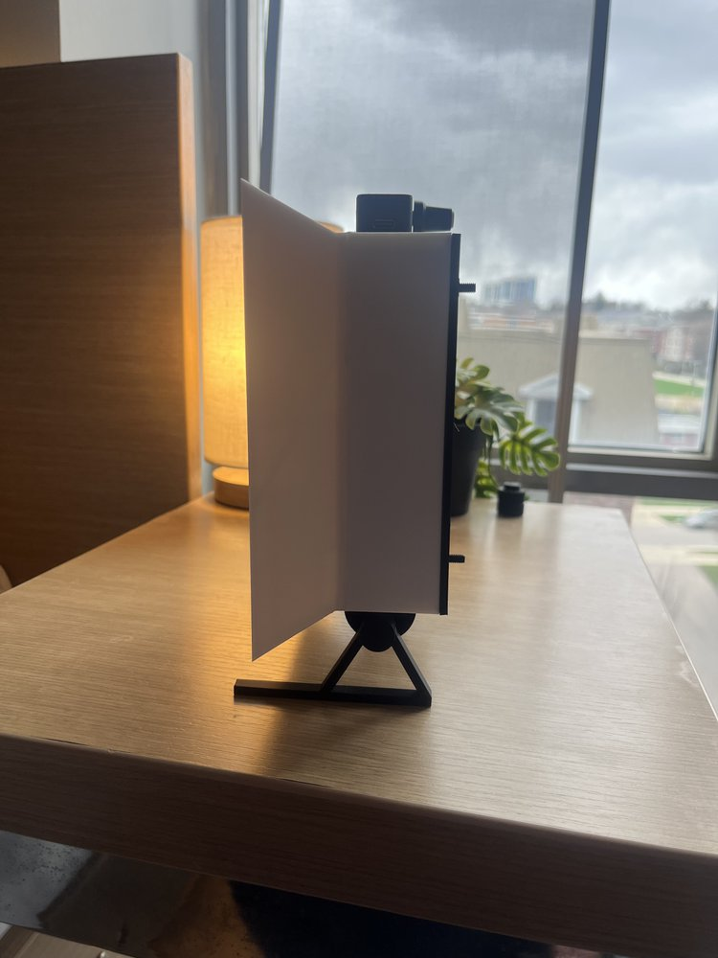
images/IMG_6753.jpeg
