AriaAbd1/Fume-Extracter/images/IMG_6756.jpeg

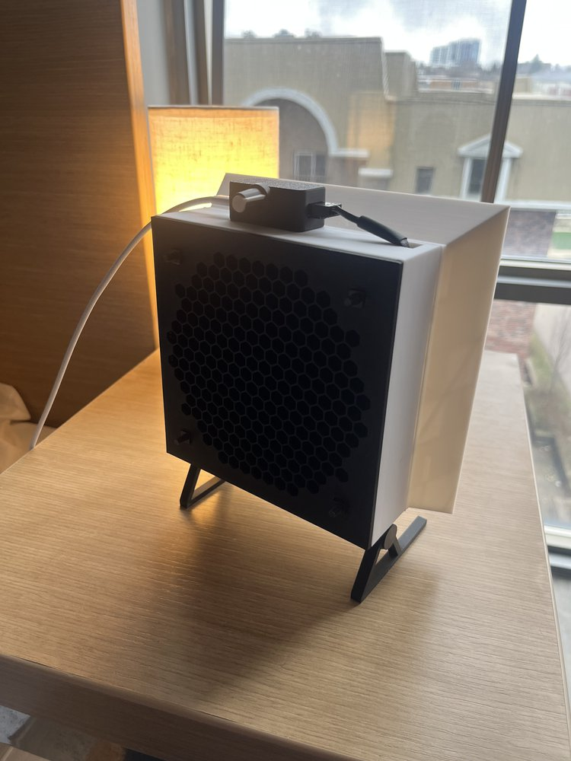
images/IMG_6756.jpeg
