AriaAbd1/Fume-Extracter/images/IMG_6757.jpeg

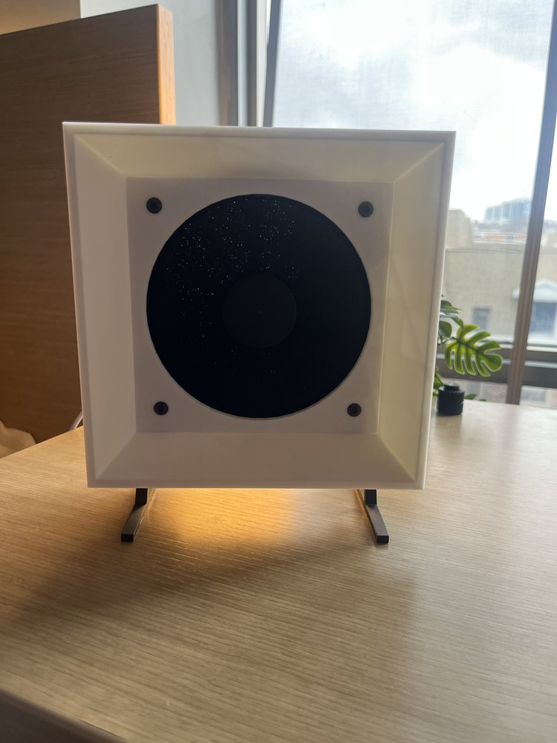
images/IMG_6757.jpeg
