AriaAbd1/Fume-Extracter/images/IMG_6758.jpeg

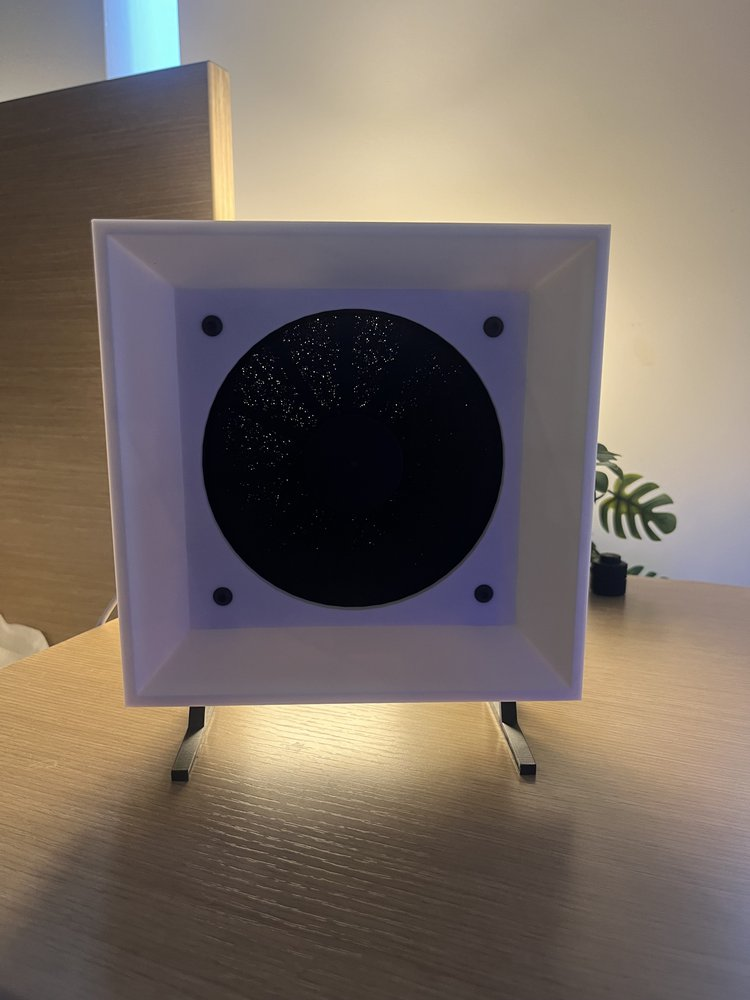
images/IMG_6758.jpeg
