AriaAbd1/Fume-Extracter/images/IMG_6759.jpeg

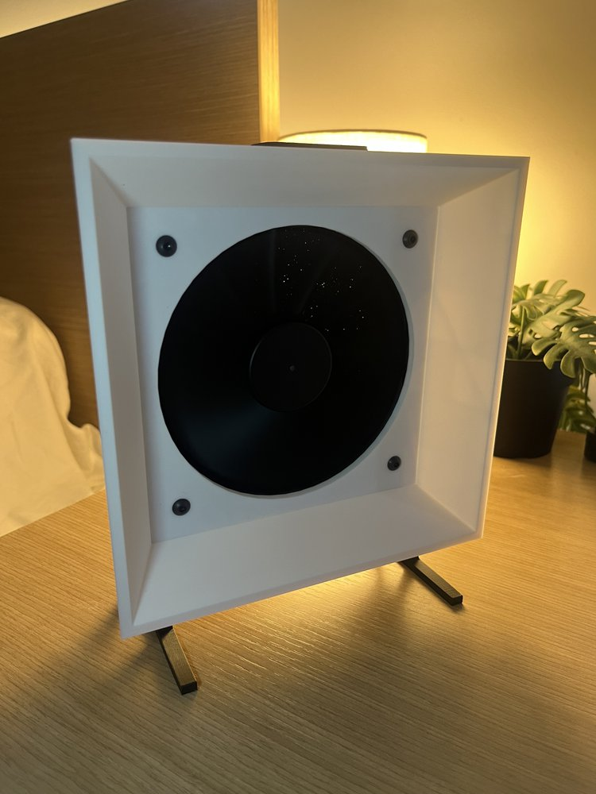
images/IMG_6759.jpeg
