AriaAbd1/Fume-Extracter/images/IMG_6760.jpeg

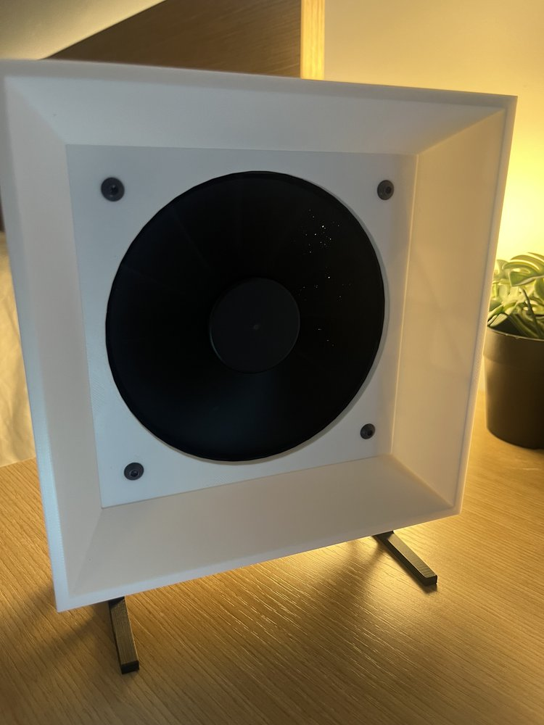
images/IMG_6760.jpeg
